hacklabmikkeli/workshop-robots/raspirobot_spacer2.scad

use <raspirobot.scad>

spacer2();
