hacklabmikkeli/workshop-robots/raspirobot_tube.scad

use <raspirobot.scad>

tubes();
