hacklabmikkeli/workshop-robots/servo.scad

module servo() {
    scale([1,1,1])
    rotate([63,33,-5])
    import("servomotor_1.stl");
}

servo();
