hacklabmikkeli/workshop-robots/servo_tire.scad

difference() {
    color("green") cylinder(d=45.5, h=4.5, center=true);
    color("red") cylinder(d=42.5, h=2.5, center=true);
    color("black") cylinder(d=38.5, h=5, center=true);
}
